KLFAMO/relock_Artiq/kicad/AD DA module.kicad_sch

## KiCad design kicad/AD DA module.kicad_sch (2025-12-02)

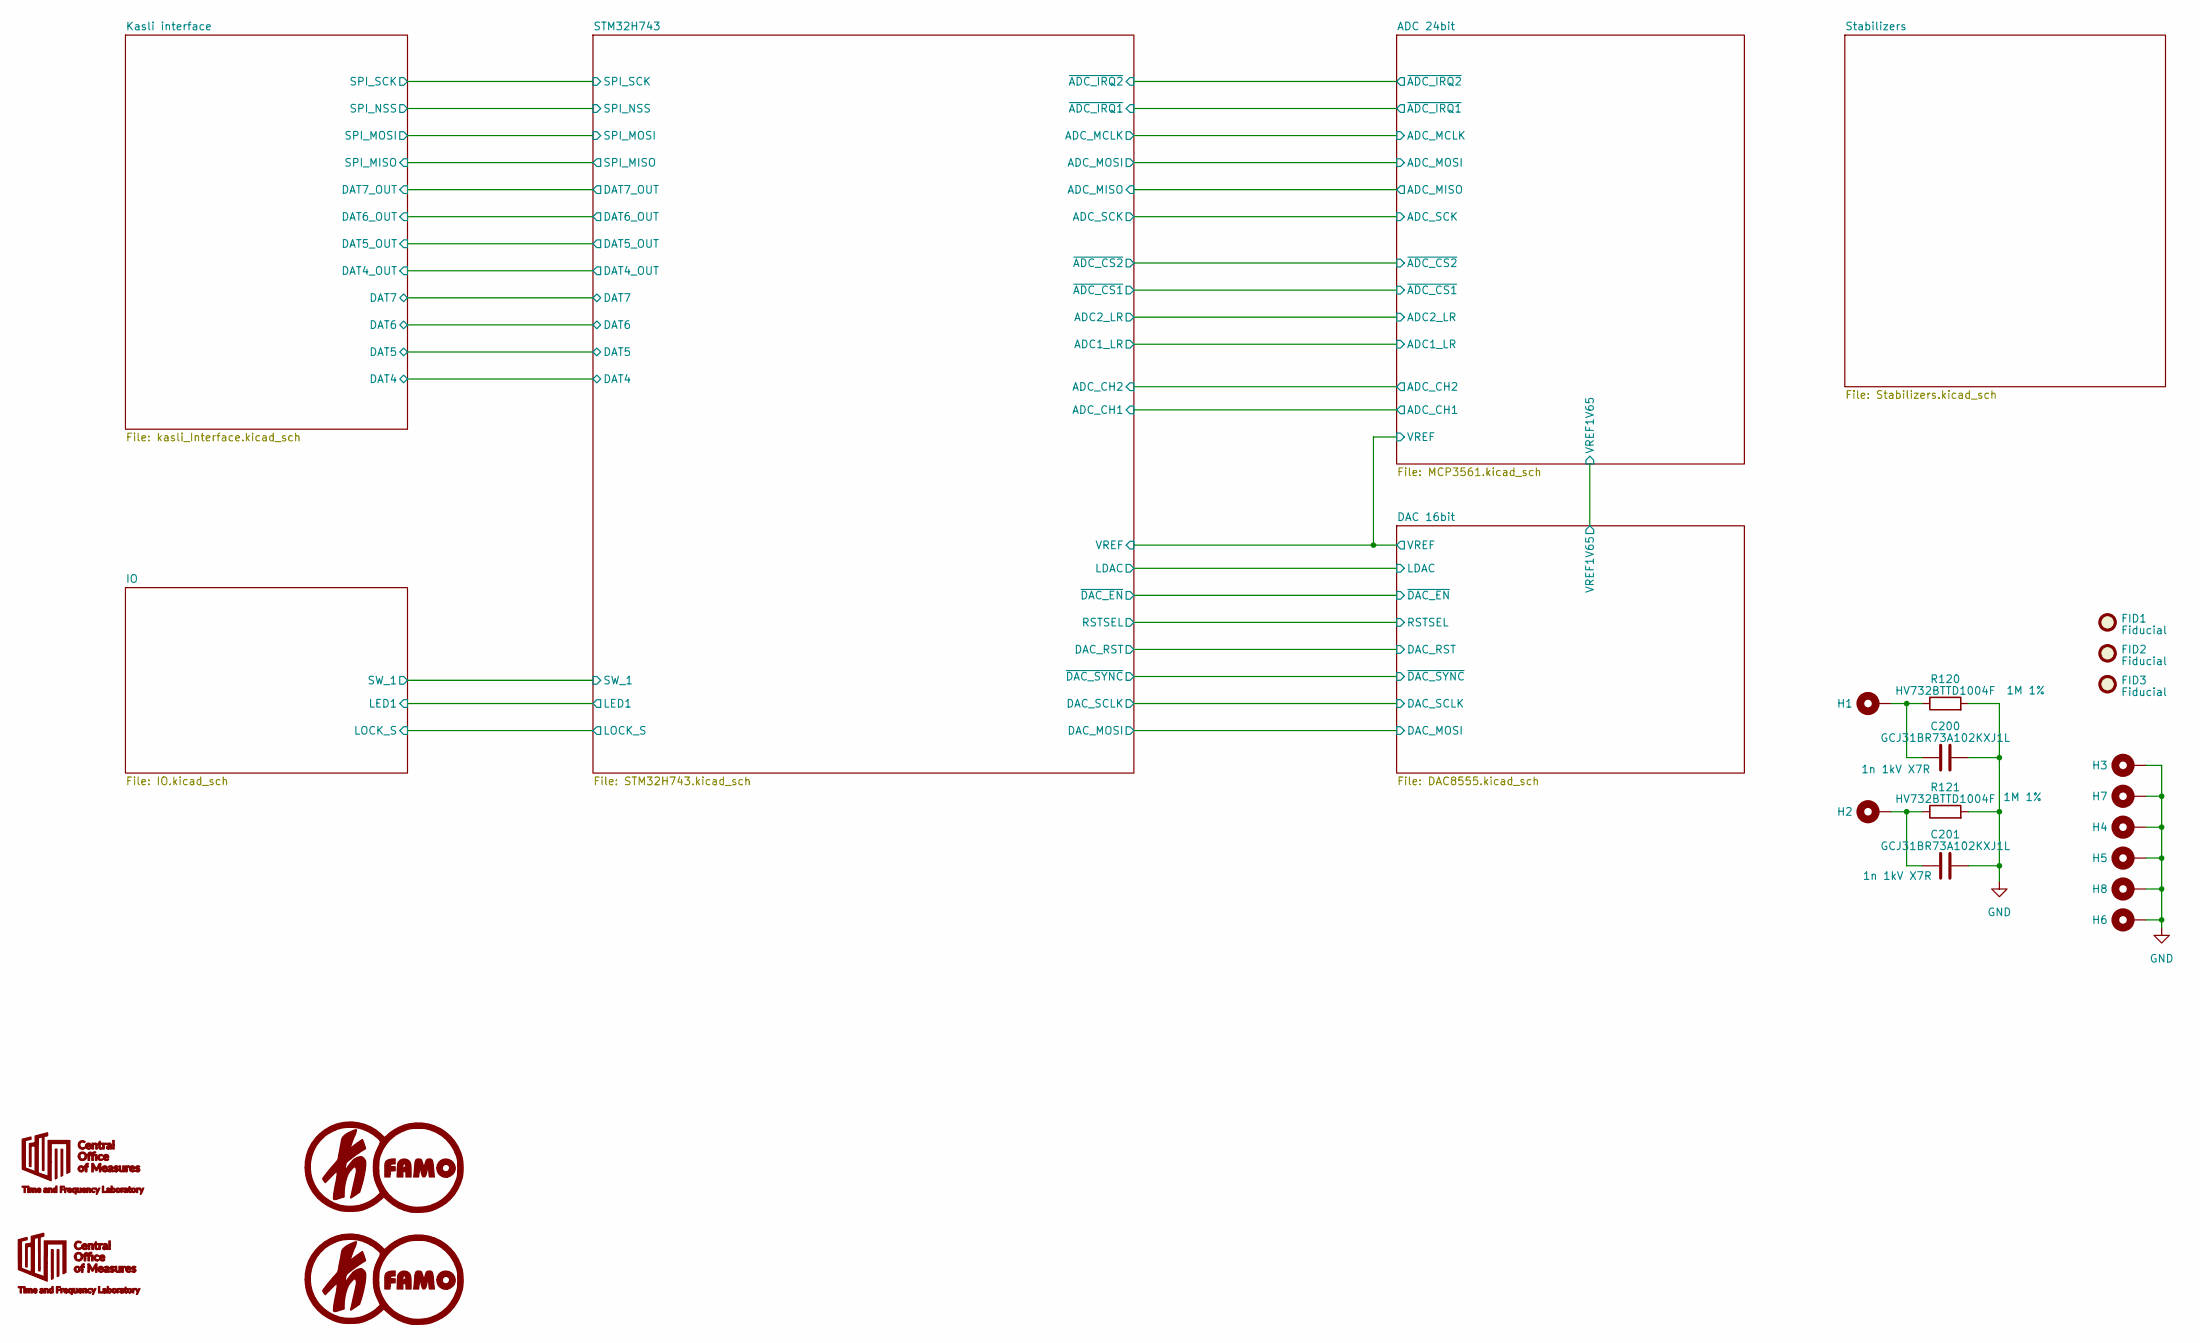
[picture p2: schematic AD DA module.kicad_sch]

Parts:
C200, C201: GCJ31BR73A102KXJ1L; C_1206_3216Metric
FID1, FID2, FID3: Fiducial; Fiducial_0.5mm_Mask1.5mm
G1, G2: LOGO; GUM_logo
G3, G4: LOGO; kl_famo_logo_small
H1, H2: MountingHole_Pad; MountingHole_2.7mm_M2.5_DIN965_Pad
H3, H4, H5, H6, H7, H8: MountingHole_Pad; MountingHole_3.2mm_M3_DIN965_Pad
R120, R121: HV732BTTD1004F; R_1206_3216Metric

Connections:
GND: C200.2, C201.2, H3.1, H4.1, H5.1, H6.1, H7.1, H8.1, R120.2, R121.2
unnamed: C200.1, H1.1, R120.1
unnamed: C201.1, H2.1, R121.1
