KLFAMO/relock_Artiq/kicad/DAC8555.kicad_sch

## KiCad design kicad/DAC8555.kicad_sch (2025-12-02)

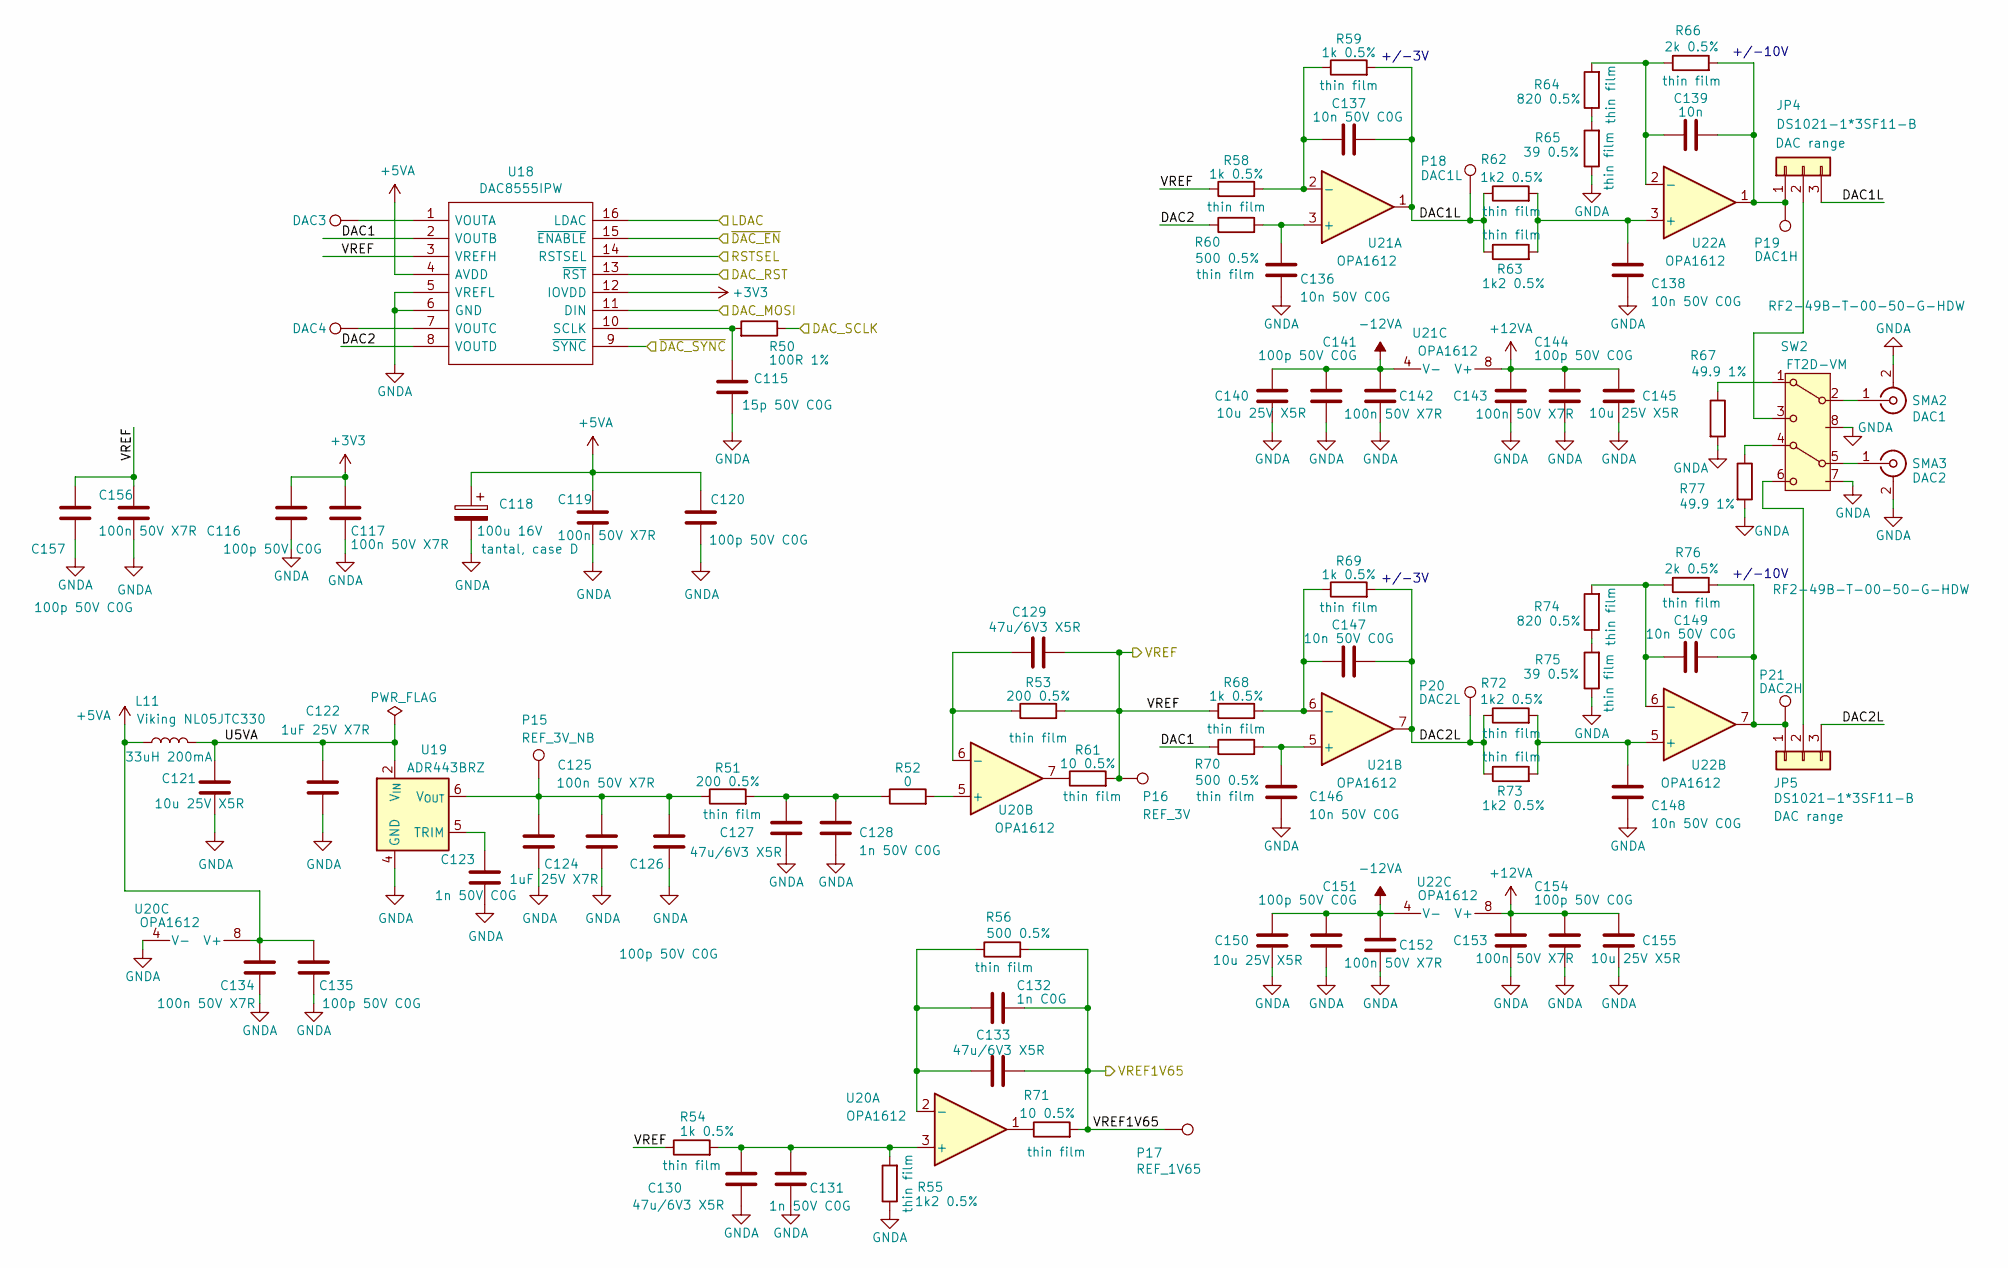
[picture p3: schematic DAC8555.kicad_sch]

Parts:
C115: 15p 50V C0G; C_0603_1608Metric
C116, C120, C126, C135, C141, C144, C151, C154, C157: 100p 50V C0G; C_0603_1608Metric
C117, C119, C125, C134, C142, C143, C152, C153, C156: 100n 50V X7R; C_0603_1608Metric
C118: 100u 16V; CP_EIA-7343-31_Kemet-D
C121, C140, C145, C150, C155: GRM188R61E106KA73D; C_0603_1608Metric
C122, C124: GCM188R71E105KA64J; C_0603_1608Metric
C123, C128, C131: 1n 50V C0G; C_0603_1608Metric
C127, C129, C130, C133: GRM188R60J476ME15D; C_0603_1608Metric
C132: 1n C0G; C_0603_1608Metric
C136, C137, C138, C146, C147, C148, C149: 10n 50V C0G; C_0603_1608Metric
C139: 10n; C_0603_1608Metric
DAC3, DAC4: TestPoint; TestPoint_THTPad_1.5x1.5mm_Drill0.7mm
JP4, JP5: DS1021-1*3SF11-B; PinHeader_1x03_P2.54mm_Vertical
L11: Viking NL05JTC330; L_0805_2012Metric
P15: REF_3V_NB; TestPoint_THTPad_1.5x1.5mm_Drill0.7mm
P16: REF_3V; TestPoint_THTPad_1.5x1.5mm_Drill0.7mm
P17: REF_1V65; TestPoint_THTPad_1.5x1.5mm_Drill0.7mm
P18: DAC1L; TestPoint_THTPad_1.5x1.5mm_Drill0.7mm
P19: DAC1H; TestPoint_THTPad_1.5x1.5mm_Drill0.7mm
P20: DAC2L; TestPoint_THTPad_1.5x1.5mm_Drill0.7mm
P21: DAC2H; TestPoint_THTPad_1.5x1.5mm_Drill0.7mm
R50: 100R 1%; R_0603_1608Metric
R51, R53: 200 0.5%; R_0805_2012Metric_Pad1.20x1.40mm_HandSolder
R52: 0; R_0603_1608Metric
R54, R58, R59, R68, R69: 1k 0.5%; R_0805_2012Metric_Pad1.20x1.40mm_HandSolder
R55, R62, R63, R72, R73: 1k2 0.5%; R_0805_2012Metric_Pad1.20x1.40mm_HandSolder
R56, R60, R70: 500 0.5%; R_0805_2012Metric_Pad1.20x1.40mm_HandSolder
R61, R71: 10 0.5%; R_0805_2012Metric_Pad1.20x1.40mm_HandSolder
R64, R74: 820 0.5%; R_0805_2012Metric_Pad1.20x1.40mm_HandSolder
R65, R75: 39 0.5%; R_0805_2012Metric_Pad1.20x1.40mm_HandSolder
R66, R76: 2k 0.5%; R_0805_2012Metric_Pad1.20x1.40mm_HandSolder
R67, R77: 49.9 1%; R_0603_1608Metric
SMA2, SMA3: RF2-49B-T-00-50-G-HDW; SMA_Amphenol_901-143_Horizontal
SW2: FT2D-VM
U18: DAC8555IPW; TSSOP-16_4.4x5mm_P0.65mm
U19: ADR443BRZ; SOIC-8_3.9x4.9mm_P1.27mm
U20, U21, U22: OPA1612; SOIC-8_3.9x4.9mm_P1.27mm

Connections:
+3V3: C116.1, C117.1, U18.12 (IOVDD)
+5VA: C118.1, C119.1, C120.1, C134.1, C135.1, L11.1, U18.4 (AVDD), U20.8 (V+)
+12VA: C143.1, C144.1, C145.1, C153.1, C154.1, C155.1, U21.8 (V+), U22.8 (V+)
-12VA: C140.1, C141.1, C142.1, C150.1, C151.1, C152.1, U21.4 (V-), U22.4 (V-)
DAC1: R70.1, U18.2 (VOUTB)
DAC1L: C137.2, JP4.3, P18.1, R59.2, R62.1, R63.1, U21.1
DAC2: R60.1, U18.8 (VOUTD)
DAC2L: C147.2, JP5.3, P20.1, R69.2, R72.1, R73.1, U21.7
DAC_MOSI: U18.11 (DIN)
DAC_RST: U18.13 (~RST)
DAC_SCLK: R50.1
GNDA: C115.2, C116.2, C117.2, C118.2, C119.2, C120.2, C121.2, C122.2, C123.1, C124.2, C125.2, C126.2, C127.1, C128.2, C130.1, C131.2, C134.2, C135.2, C136.1, C138.1, C140.2, C141.2, C142.2, C143.2, C144.2, C145.2, C146.1, C148.1, C150.2, C151.2, C152.2, C153.2, C154.2, C155.2, C156.2, C157.2, R55.1, R65.1, R67.2, R75.1, R77.2, SMA2.2 (Ext), SMA3.2 (Ext), SW2.7, SW2.8, U18.5 (VREFL), U18.6 (GND), U19.4 (GND), U20.4 (V-)
LDAC: U18.16 (LDAC)
unnamed: C115.1, R50.2, U18.10 (SCLK)
unnamed: C123.2, U19.5 (TRIM)
unnamed: C124.1, C125.1, C126.1, P15.1, R51.1, U19.6 (V_{OUT})
unnamed: C127.2, C128.1, R51.2, R52.1
unnamed: C129.2, R53.1, U20.6 (-)
unnamed: C130.2, C131.1, R54.2, R55.2, U20.3 (+)
unnamed: C132.1, C133.2, R56.1, U20.2 (-)
unnamed: C136.2, R60.2, U21.3 (+)
unnamed: C137.1, R58.2, R59.1, U21.2 (-)
unnamed: C138.2, R62.2, R63.2, U22.3 (+)
unnamed: C139.1, R64.2, R66.1, U22.2 (-)
unnamed: C139.2, JP4.1, P19.1, R66.2, U22.1
unnamed: C146.2, R70.2, U21.5 (+)
unnamed: C147.1, R68.2, R69.1, U21.6 (-)
unnamed: C148.2, R72.2, R73.2, U22.5 (+)
unnamed: C149.1, R74.2, R76.1, U22.6 (-)
unnamed: C149.2, JP5.1, P21.1, R76.2, U22.7
unnamed: DAC3.1, U18.1 (VOUTA)
unnamed: DAC4.1, U18.7 (VOUTC)
unnamed: JP4.2, SW2.3
unnamed: JP5.2, SW2.6
unnamed: R52.2, U20.5 (+)
unnamed: R61.1, U20.7
unnamed: R64.1, R65.2
unnamed: R67.1, SW2.1
unnamed: R71.1, U20.1
unnamed: R74.1, R75.2
unnamed: R77.1, SW2.4
unnamed: SMA2.1 (In), SW2.2
unnamed: SMA3.1 (In), SW2.5
RSTSEL: U18.14 (RSTSEL)
U5VA: C121.1, C122.1, L11.2, U19.2 (V_{IN})
VREF: C129.1, C156.1, C157.1, P16.1, R53.2, R54.1, R58.1, R61.2, R68.1, U18.3 (VREFH)
VREF1V65: C132.2, C133.1, P17.1, R56.2, R71.2
~DAC_EN: U18.15 (~ENABLE)
~DAC_SYNC: U18.9 (~SYNC)

Notes on the sheet:
+/-3V
+/-10V
