KLFAMO/relock_Artiq/kicad/IO.kicad_sch

## KiCad design kicad/IO.kicad_sch (2025-12-02)

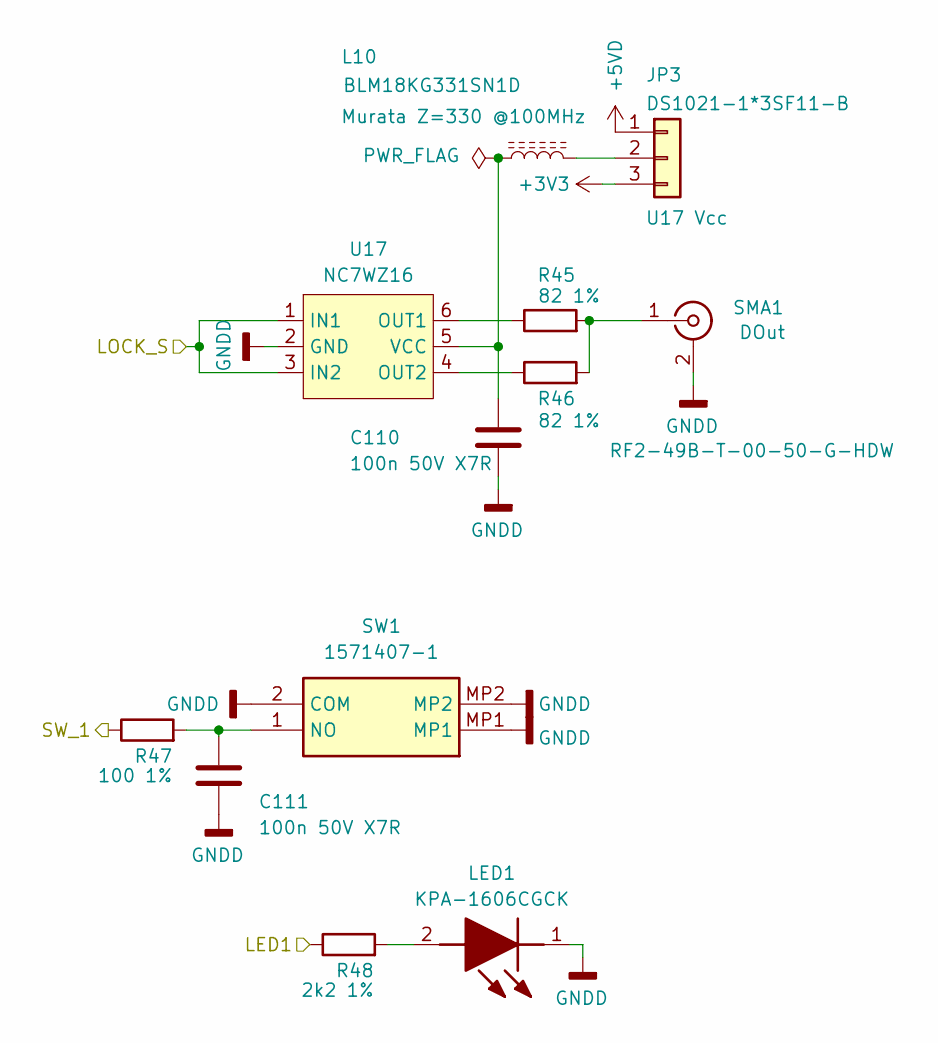
[picture p4: schematic IO.kicad_sch]

Parts:
C110, C111: 100n 50V X7R; C_0603_1608Metric
JP3: DS1021-1*3SF11-B; PinHeader_1x03_P2.54mm_Vertical
L10: BLM18KG331SN1D; L_0603_1608Metric
LED1: KPA-1606CGCK; KPA1606CGCK
R45, R46: 82 1%; R_0603_1608Metric
R47: 100 1%; R_0603_1608Metric
R48: 2k2 1%; R_0603_1608Metric
SMA1: RF2-49B-T-00-50-G-HDW; SMA_Amphenol_901-143_Horizontal
SW1: 1571407-1; 15714071; Manufacturer_Part_Number 1571407-1
U17: NC7WZ16; SOT65P215X100-6N

Connections:
+3V3: JP3.3
+5VD: JP3.1
GNDD: C110.2, C111.2, LED1.1 (K), SMA1.2 (Ext), SW1.2 (COM), SW1.MP1, SW1.MP2, U17.2 (GND)
LED1: R48.1
LOCK_S: U17.1 (IN1), U17.3 (IN2)
unnamed: C110.1, L10.1, U17.5 (VCC)
unnamed: C111.1, R47.2, SW1.1 (NO)
unnamed: JP3.2, L10.2
unnamed: LED1.2 (A), R48.2
unnamed: R45.1, U17.6 (OUT1)
unnamed: R45.2, R46.2, SMA1.1 (In)
unnamed: R46.1, U17.4 (OUT2)
SW_1: R47.1
