KLFAMO/relock_Artiq/kicad/MCP3561.kicad_sch

## KiCad design kicad/MCP3561.kicad_sch (2025-12-02)

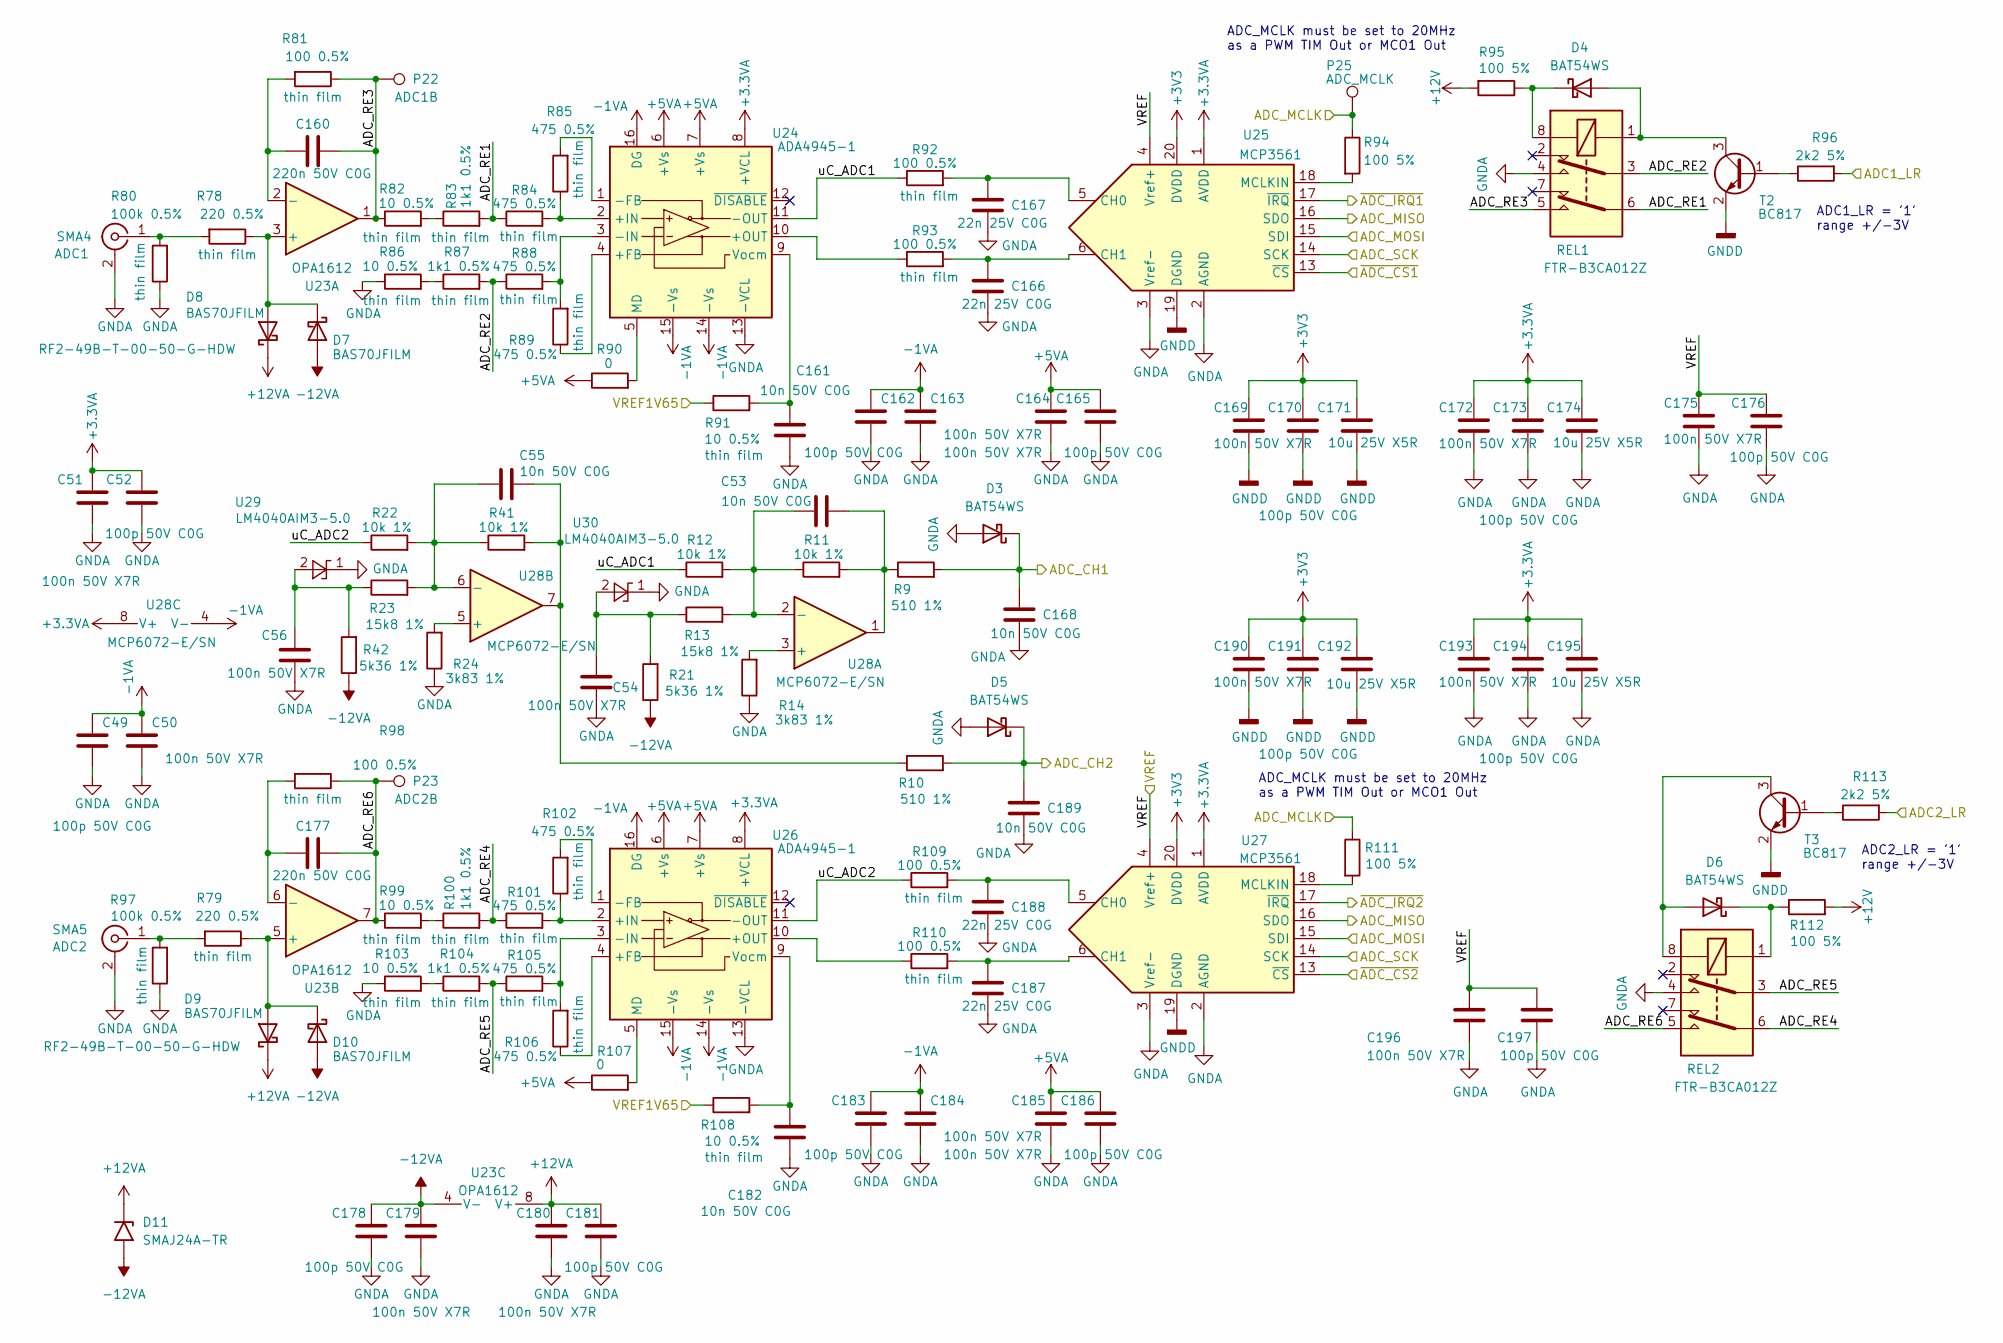
[picture p5: schematic MCP3561.kicad_sch]

Parts:
C49, C52, C162, C165, C170, C173, C176, C178, C181, C183, C186, C191, C194, C197: 100p 50V C0G; C_0603_1608Metric
C50, C51, C54, C56, C163, C164, C169, C172, C175, C179, C180, C184, C185, C190, C193, C196: 100n 50V X7R; C_0603_1608Metric
C53, C55, C161, C168, C182, C189: 10n 50V C0G; C_0603_1608Metric
C160, C177: 220n 50V C0G; C_1206_3216Metric
C166, C167, C187, C188: 22n 25V C0G; C_0603_1608Metric
C171, C174, C192, C195: GRM188R61E106KA73D; C_0603_1608Metric
D3, D4, D5, D6: BAT54WS; D_SOD-323F
D7, D8, D9, D10: BAS70JFILM; D_SOD-323F
D11: SMAJ24A-TR; D_SMA
P22: ADC1B; TestPoint_THTPad_1.5x1.5mm_Drill0.7mm
P23: ADC2B; TestPoint_THTPad_1.5x1.5mm_Drill0.7mm
P25: ADC_MCLK; TestPoint_THTPad_1.5x1.5mm_Drill0.7mm
R9, R10: 510 1%; R_0603_1608Metric
R11, R12, R22, R41: 10k 1%; R_0603_1608Metric
R13, R23: 15k8 1%; R_0603_1608Metric
R14, R24: 3k83 1%; R_0603_1608Metric
R21, R42: 5k36 1%; R_0603_1608Metric
R78, R79: 220 0.5%; R_0603_1608Metric_Pad0.98x0.95mm_HandSolder
R80, R97: 100k 0.5%; R_0805_2012Metric_Pad1.20x1.40mm_HandSolder
R81, R98: 100 0.5%; R_0603_1608Metric_Pad0.98x0.95mm_HandSolder
R82, R86, R91, R99, R103, R108: 10 0.5%; R_0805_2012Metric_Pad1.20x1.40mm_HandSolder
R83, R87, R100, R104: 1k1 0.5%; R_0805_2012Metric_Pad1.20x1.40mm_HandSolder
R84, R85, R88, R89, R101, R102, R105, R106: 475 0.5%; R_0805_2012Metric_Pad1.20x1.40mm_HandSolder
R90, R107: 0; R_0603_1608Metric
R92, R93, R109, R110: 100 0.5%; R_0805_2012Metric_Pad1.20x1.40mm_HandSolder
R94, R111: 100 5%; R_0603_1608Metric
R95, R112: 100 5%; R_1206_3216Metric
R96, R113: 2k2 5%; R_0603_1608Metric
REL1, REL2: FTR-B3CA012Z; FTRB3CA012Z
SMA4, SMA5: RF2-49B-T-00-50-G-HDW; SMA_Amphenol_901-143_Horizontal
T2, T3: BC817; SOT-23
U23: OPA1612; SOIC-8_3.9x4.9mm_P1.27mm
U24, U26: ADA4945-1; LFCSP-16-1EP_3x3mm_P0.5mm_EP1.6x1.6mm_ThermalVias
U25, U27: MCP3561; SSOP-20_4.4x6.5mm_P0.65mm
U28: MCP6072-E/SN; SOIC-8_3.9x4.9mm_P1.27mm
U29, U30: LM4040AIM3-5.0; SOT-23

Connections:
+3.3VA: C51.1, C52.2, C172.1, C173.1, C174.1, C193.1, C194.1, C195.1, U24.8 (+VCL), U25.1 (AVDD), U26.8 (+VCL), U27.1 (AVDD), U28.8 (V+)
+3V3: C169.1, C170.1, C171.1, C190.1, C191.1, C192.1, U25.20 (DVDD), U27.20 (DVDD)
+5VA: C164.1, C165.2, C185.1, C186.2, R90.1, R107.1, U24.6 (+Vs), U24.7 (+Vs), U26.6 (+Vs), U26.7 (+Vs)
+12V: R95.2, R112.2
+12VA: C180.1, C181.2, D8.1 (K), D9.1 (K), D11.1 (A1), U23.8 (V+)
-1VA: C49.2, C50.1, C162.2, C163.1, C183.2, C184.1, U24.14 (-Vs), U24.15 (-Vs), U24.16 (DG), U24.17 (-Vs), U26.14 (-Vs), U26.15 (-Vs), U26.16 (DG), U26.17 (-Vs), U28.4 (V-)
-12VA: C178.2, C179.1, D7.2 (A), D10.2 (A), D11.2 (A2), R21.1, R42.1, U23.4 (V-)
ADC1_LR: R96.2
ADC2_LR: R113.2
ADC_CH1: C168.2, D3.1 (K), R9.2
ADC_CH2: C189.2, D5.1 (K), R10.2
ADC_MCLK: P25.1, R94.1, R111.1
ADC_MISO: U25.16 (SDO), U27.16 (SDO)
ADC_MOSI: U25.15 (SDI), U27.15 (SDI)
ADC_RE1: R83.2, R84.1, REL1.6
ADC_RE2: R87.2, R88.1, REL1.3
ADC_RE3: C160.2, P22.1, R81.1, R82.1, REL1.5, U23.1
ADC_RE4: R100.2, R101.1, REL2.6
ADC_RE5: R104.2, R105.1, REL2.3
ADC_RE6: C177.2, P23.1, R98.1, R99.1, REL2.5, U23.7
ADC_SCK: U25.14 (SCK), U27.14 (SCK)
GNDA: C49.1, C50.2, C51.2, C52.1, C54.2, C56.2, C161.2, C162.1, C163.2, C164.2, C165.1, C166.1, C167.1, C168.1, C172.2, C173.2, C174.2, C175.2, C176.2, C178.1, C179.2, C180.2, C181.1, C182.2, C183.1, C184.2, C185.2, C186.1, C187.1, C188.1, C189.1, C193.2, C194.2, C195.2, C196.2, C197.2, D3.2 (A), D5.2 (A), R14.1, R24.1, R80.1, R86.1, R97.1, R103.1, REL1.4, REL2.4, SMA4.2 (Ext), SMA5.2 (Ext), U24.13 (-VCL), U25.2 (AGND), U25.3 (Vref-), U26.13 (-VCL), U27.2 (AGND), U27.3 (Vref-), U29.1 (K), U30.1 (K)
GNDD: C169.2, C170.2, C171.2, C190.2, C191.2, C192.2, T2.2 (E), T3.2 (E), U25.19 (DGND), U27.19 (DGND)
unnamed: C53.1, R9.1, R11.2, U28.1
unnamed: C53.2, R11.1, R12.2, R13.2, U28.2 (-)
unnamed: C54.1, R13.1, R21.2, U30.2 (A)
unnamed: C55.1, R10.1, R41.2, U28.7
unnamed: C55.2, R22.2, R23.2, R41.1, U28.6 (-)
unnamed: C56.1, R23.1, R42.2, U29.2 (A)
unnamed: C160.1, R81.2, U23.2 (-)
unnamed: C161.1, R91.2, U24.9 (Vocm)
unnamed: C166.2, R93.2, U25.6 (CH1)
unnamed: C167.2, R92.2, U25.5 (CH0)
unnamed: C177.1, R98.2, U23.6 (-)
unnamed: C182.1, R108.2, U26.9 (Vocm)
unnamed: C187.2, R110.2, U27.6 (CH1)
unnamed: C188.2, R109.2, U27.5 (CH0)
unnamed: D4.1 (K), R95.1, REL1.8
unnamed: D4.2 (A), REL1.1, T2.3 (C)
unnamed: D6.1 (K), R112.1, REL2.1
unnamed: D6.2 (A), REL2.8, T3.3 (C)
unnamed: D7.1 (K), D8.2 (A), R78.1, U23.3 (+)
unnamed: D9.2 (A), D10.1 (K), R79.1, U23.5 (+)
unnamed: R14.2, U28.3 (+)
unnamed: R24.2, U28.5 (+)
unnamed: R78.2, R80.2, SMA4.1 (In)
unnamed: R79.2, R97.2, SMA5.1 (In)
unnamed: R82.2, R83.1
unnamed: R84.2, R85.1, U24.2 (+IN)
unnamed: R85.2, U24.1 (-FB)
unnamed: R86.2, R87.1
unnamed: R88.2, R89.2, U24.3 (-IN)
unnamed: R89.1, U24.4 (+FB)
unnamed: R90.2, U24.5 (MD)
unnamed: R93.1, U24.10 (+OUT)
unnamed: R94.2, U25.18 (MCLKIN)
unnamed: R96.1, T2.1 (B)
unnamed: R99.2, R100.1
unnamed: R101.2, R102.1, U26.2 (+IN)
unnamed: R102.2, U26.1 (-FB)
unnamed: R103.2, R104.1
unnamed: R105.2, R106.2, U26.3 (-IN)
unnamed: R106.1, U26.4 (+FB)
unnamed: R107.2, U26.5 (MD)
unnamed: R110.1, U26.10 (+OUT)
unnamed: R111.2, U27.18 (MCLKIN)
unnamed: R113.1, T3.1 (B)
VREF: C175.1, C176.1, C196.1, C197.1, U25.4 (Vref+), U27.4 (Vref+)
VREF1V65: R91.1, R108.1
uC_ADC1: R12.1, R92.1, U24.11 (-OUT)
uC_ADC2: R22.1, R109.1, U26.11 (-OUT)
~ADC_CS1: U25.13 (~CS)
~ADC_CS2: U27.13 (~CS)
~ADC_IRQ1: U25.17 (~IRQ)
~ADC_IRQ2: U27.17 (~IRQ)

Notes on the sheet:
ADC2_LR = '1' range +/-3V
ADC_MCLK must be set to 20MHz as a PWM TIM Out or MCO1 Out
ADC1_LR = '1' range +/-3V
