KLFAMO/relock_Artiq/kicad/STM32H743.kicad_sch

## KiCad design kicad/STM32H743.kicad_sch (2025-12-02)

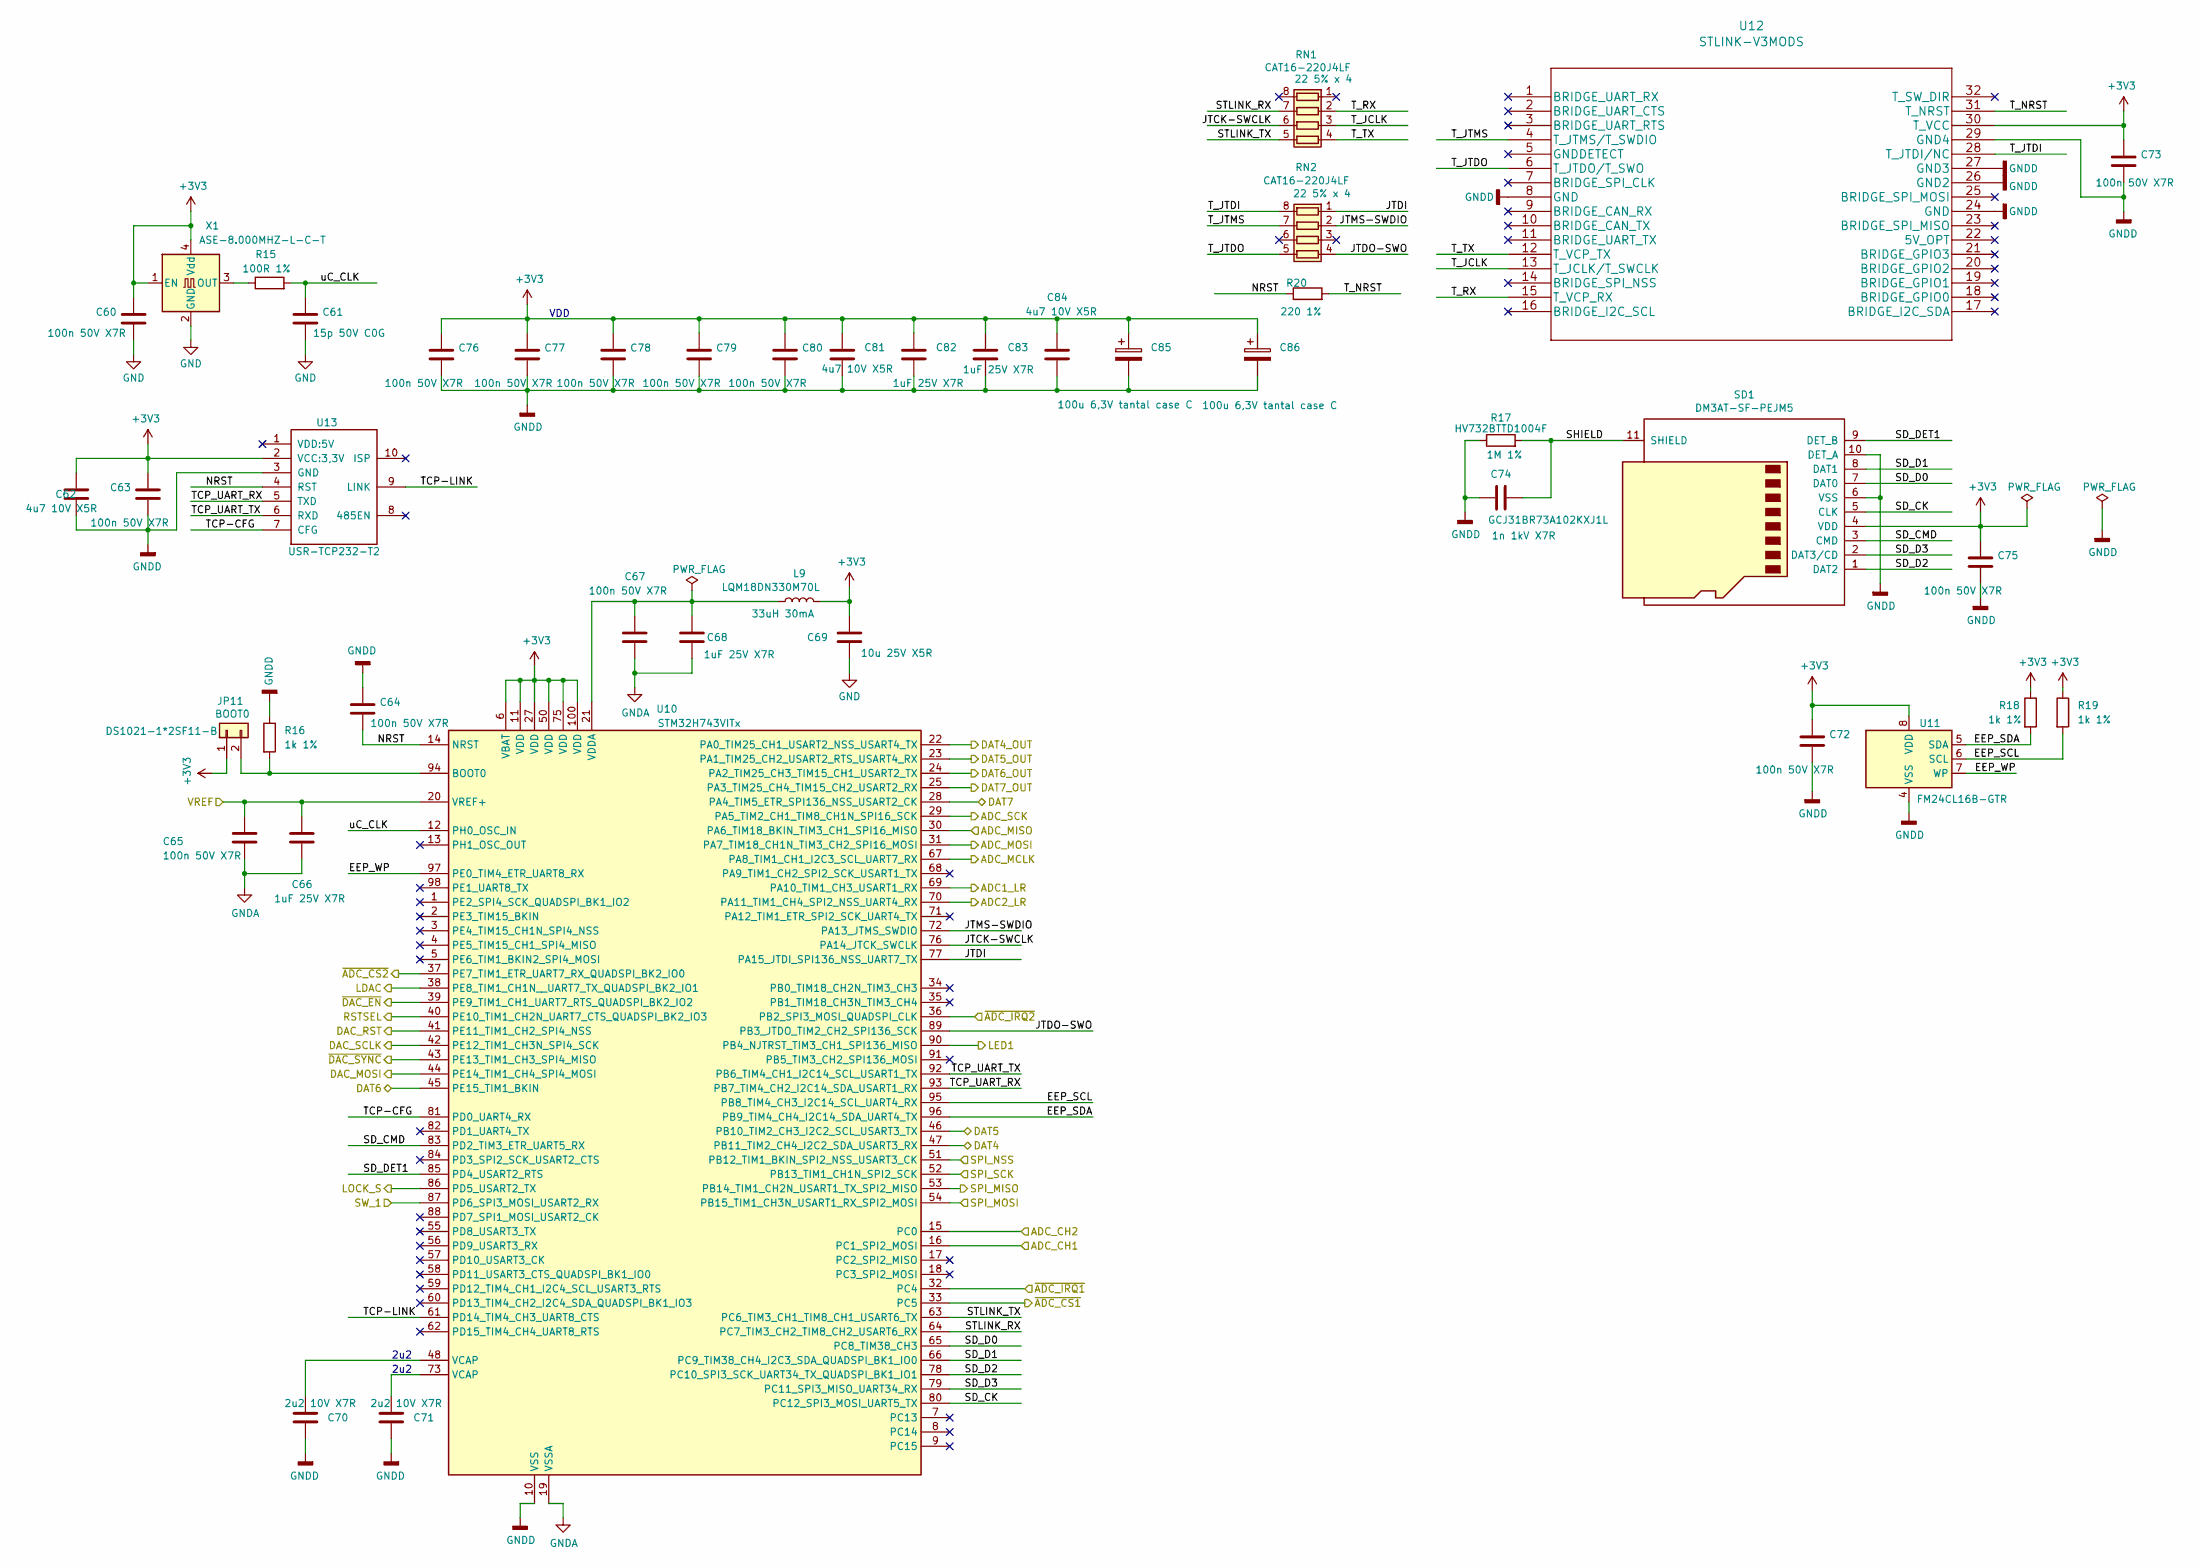
[picture p6: schematic STM32H743.kicad_sch]

Parts:
C60, C63, C64, C65, C67, C72, C73, C75, C76, C77, C78, C79, C80: 100n 50V X7R; C_0603_1608Metric
C61: 15p 50V C0G; C_0603_1608Metric
C62, C81, C84: 4u7 10V X5R; C_0603_1608Metric
C66, C68, C82, C83: GCM188R71E105KA64J; C_0603_1608Metric
C69: GRM188R61E106KA73D; C_0603_1608Metric
C70, C71: 2u2 10V X7R; C_0603_1608Metric
C74: GCJ31BR73A102KXJ1L; C_1206_3216Metric
C85, C86: 293D107X9010C2TE3; CP_EIA-7132-28_AVX-C
JP11: DS1021-1*2SF11-B; PinHeader_1x02_P2.54mm_Vertical
L9: LQM18DN330M70L; L_0603_1608Metric
R15: 100R 1%; R_0603_1608Metric
R16, R18, R19: 1k 1%; R_0603_1608Metric
R17: HV732BTTD1004F; R_1206_3216Metric
R20: 220 1%; R_0603_1608Metric
RN1, RN2: CAT16-220J4LF; R_Array_Concave_4x0603
SD1: DM3AT-SF-PEJM5; microSD_HC_Hirose_DM3AT-SF-PEJM5
U10: STM32H743VITx; LQFP-100_14x14mm_P0.5mm
U11: FM24CL16B-GTR; SOIC-8_3.9x4.9mm_P1.27mm
U12: STLINK-V3MODS
U13: USR-TCP232-T2; USR-TC232-T2
X1: ASE-8.000MHZ-L-C-T; Oscillator_SMD_Abracon_ASE-4Pin_3.2x2.5mm

Connections:
+3V3: C60.1, C62.1, C63.1, C69.1, C72.1, C73.1, C75.1, C76.1, C77.1, C78.1, C79.1, C80.1, C81.1, C82.1, C83.1, C84.1, C85.1, C86.1, JP11.1, L9.2, R18.1, R19.1, SD1.4 (VDD), U10.6 (VBAT), U10.11 (VDD), U10.27 (VDD), U10.50 (VDD), U10.75 (VDD), U10.100 (VDD), U11.8 (VDD), U12.30 (T_VCC), U13.2 (VCC:3,3V), X1.1 (EN), X1.4 (Vdd)
ADC1_LR: U10.69 (PA10_TIM1_CH3_USART1_RX)
ADC2_LR: U10.70 (PA11_TIM1_CH4_SPI2_NSS_UART4_RX)
ADC_CH1: U10.16 (PC1_SPI2_MOSI)
ADC_CH2: U10.15 (PC0)
ADC_MCLK: U10.67 (PA8_TIM1_CH1_I2C3_SCL_UART7_RX)
ADC_MISO: U10.30 (PA6_TIM18_BKIN_TIM3_CH1_SPI16_MISO)
ADC_MOSI: U10.31 (PA7_TIM18_CH1N_TIM3_CH2_SPI16_MOSI)
ADC_SCK: U10.29 (PA5_TIM2_CH1_TIM8_CH1N_SPI16_SCK)
DAC_MOSI: U10.44 (PE14_TIM1_CH4_SPI4_MOSI)
DAC_RST: U10.41 (PE11_TIM1_CH2_SPI4_NSS)
DAC_SCLK: U10.42 (PE12_TIM1_CH3N_SPI4_SCK)
DAT4: U10.47 (PB11_TIM2_CH4_I2C2_SDA_USART3_RX)
DAT4_OUT: U10.22 (PA0_TIM25_CH1_USART2_NSS_USART4_TX)
DAT5: U10.46 (PB10_TIM2_CH3_I2C2_SCL_USART3_TX)
DAT5_OUT: U10.23 (PA1_TIM25_CH2_USART2_RTS_USART4_RX)
DAT6: U10.45 (PE15_TIM1_BKIN)
DAT6_OUT: U10.24 (PA2_TIM25_CH3_TIM15_CH1_USART2_TX)
DAT7: U10.28 (PA4_TIM5_ETR_SPI136_NSS_USART2_CK)
DAT7_OUT: U10.25 (PA3_TIM25_CH4_TIM15_CH2_USART2_RX)
EEP_SCL: R19.2, U10.95 (PB8_TIM4_CH3_I2C14_SCL_UART4_RX), U11.6 (SCL)
EEP_SDA: R18.2, U10.96 (PB9_TIM4_CH4_I2C14_SDA_UART4_TX), U11.5 (SDA)
EEP_WP: U10.97 (PE0_TIM4_ETR_UART8_RX), U11.7 (WP)
GND: C60.2, C61.2, C69.2, X1.2 (GND)
GNDA: C65.1, C66.2, C67.1, C68.2, U10.19 (VSSA)
GNDD: C62.2, C63.2, C64.1, C70.1, C71.1, C72.2, C73.2, C74.1, C75.2, C76.2, C77.2, C78.2, C79.2, C80.2, C81.2, C82.2, C83.2, C84.2, C85.2, C86.2, R16.1, R17.1, SD1.6 (VSS), SD1.10 (DET_A), U10.10 (VSS), U10.26 (VSS), U10.49 (VSS), U10.74 (VSS), U10.99 (VSS), U11.4 (VSS), U12.8 (GND), U12.24 (GND), U12.26 (GND2), U12.27 (GND3), U12.29 (GND4), U13.3 (GND)
JTCK-SWCLK: RN1.6 (R3.2), U10.76 (PA14_JTCK_SWCLK)
JTDI: RN2.1 (R1.1), U10.77 (PA15_JTDI_SPI136_NSS_UART7_TX)
JTDO-SWO: RN2.4 (R4.1), U10.89 (PB3_JTDO_TIM2_CH2_SPI136_SCK)
JTMS-SWDIO: RN2.2 (R2.1), U10.72 (PA13_JTMS_SWDIO)
LDAC: U10.38 (PE8_TIM1_CH1N__UART7_TX_QUADSPI_BK2_IO1)
LED1: U10.90 (PB4_NJTRST_TIM3_CH1_SPI136_MISO)
LOCK_S: U10.86 (PD5_USART2_TX)
NRST: C64.2, R20.1, U10.14 (NRST), U13.4 (RST)
unnamed: C67.2, C68.1, L9.1, U10.21 (VDDA)
unnamed: C70.2, U10.48 (VCAP)
unnamed: C71.2, U10.73 (VCAP)
unnamed: JP11.2, R16.2, U10.94 (BOOT0)
unnamed: R15.1, X1.3 (OUT)
RSTSEL: U10.40 (PE10_TIM1_CH2N_UART7_CTS_QUADSPI_BK2_IO3)
SD_CK: SD1.5 (CLK), U10.80 (PC12_SPI3_MOSI_UART5_TX)
SD_CMD: SD1.3 (CMD), U10.83 (PD2_TIM3_ETR_UART5_RX)
SD_D0: SD1.7 (DAT0), U10.65 (PC8_TIM38_CH3)
SD_D1: SD1.8 (DAT1), U10.66 (PC9_TIM38_CH4_I2C3_SDA_QUADSPI_BK1_IO0)
SD_D2: SD1.1 (DAT2), U10.78 (PC10_SPI3_SCK_UART34_TX_QUADSPI_BK1_IO1)
SD_D3: SD1.2 (DAT3/CD), U10.79 (PC11_SPI3_MISO_UART34_RX)
SD_DET1: SD1.9 (DET_B), U10.85 (PD4_USART2_RTS)
SHIELD: C74.2, R17.2, SD1.11 (SHIELD)
SPI_MISO: U10.53 (PB14_TIM1_CH2N_USART1_TX_SPI2_MISO)
SPI_MOSI: U10.54 (PB15_TIM1_CH3N_USART1_RX_SPI2_MOSI)
SPI_NSS: U10.51 (PB12_TIM1_BKIN_SPI2_NSS_USART3_CK)
SPI_SCK: U10.52 (PB13_TIM1_CH1N_SPI2_SCK)
STLINK_RX: RN1.7 (R2.2), U10.64 (PC7_TIM3_CH2_TIM8_CH2_USART6_RX)
STLINK_TX: RN1.5 (R4.2), U10.63 (PC6_TIM3_CH1_TIM8_CH1_USART6_TX)
SW_1: U10.87 (PD6_SPI3_MOSI_USART2_RX)
TCP-CFG: U10.81 (PD0_UART4_RX), U13.7 (CFG)
TCP-LINK: U10.61 (PD14_TIM4_CH3_UART8_CTS), U13.9 (LINK)
TCP_UART_RX: U10.93 (PB7_TIM4_CH2_I2C14_SDA_USART1_RX), U13.5 (TXD)
TCP_UART_TX: U10.92 (PB6_TIM4_CH1_I2C14_SCL_USART1_TX), U13.6 (RXD)
T_JCLK: RN1.3 (R3.1), U12.13 (T_JCLK/T_SWCLK)
T_JTDI: RN2.8 (R1.2), U12.28 (T_JTDI/NC)
T_JTDO: RN2.5 (R4.2), U12.6 (T_JTDO/T_SWO)
T_JTMS: RN2.7 (R2.2), U12.4 (T_JTMS/T_SWDIO)
T_NRST: R20.2, U12.31 (T_NRST)
T_RX: RN1.2 (R2.1), U12.15 (T_VCP_RX)
T_TX: RN1.4 (R4.1), U12.12 (T_VCP_TX)
VREF: C65.2, C66.1, U10.20 (VREF+)
uC_CLK: C61.1, R15.2, U10.12 (PH0_OSC_IN)
~ADC_CS1: U10.33 (PC5)
~ADC_CS2: U10.37 (PE7_TIM1_ETR_UART7_RX_QUADSPI_BK2_IO0)
~ADC_IRQ1: U10.32 (PC4)
~ADC_IRQ2: U10.36 (PB2_SPI3_MOSI_QUADSPI_CLK)
~DAC_EN: U10.39 (PE9_TIM1_CH1_UART7_RTS_QUADSPI_BK2_IO2)
~DAC_SYNC: U10.43 (PE13_TIM1_CH3_SPI4_MISO)

Notes on the sheet:
2u2
VDD
