KLFAMO/relock_Artiq/kicad/Stabilizers.kicad_sch

## KiCad design kicad/Stabilizers.kicad_sch (2025-12-02)

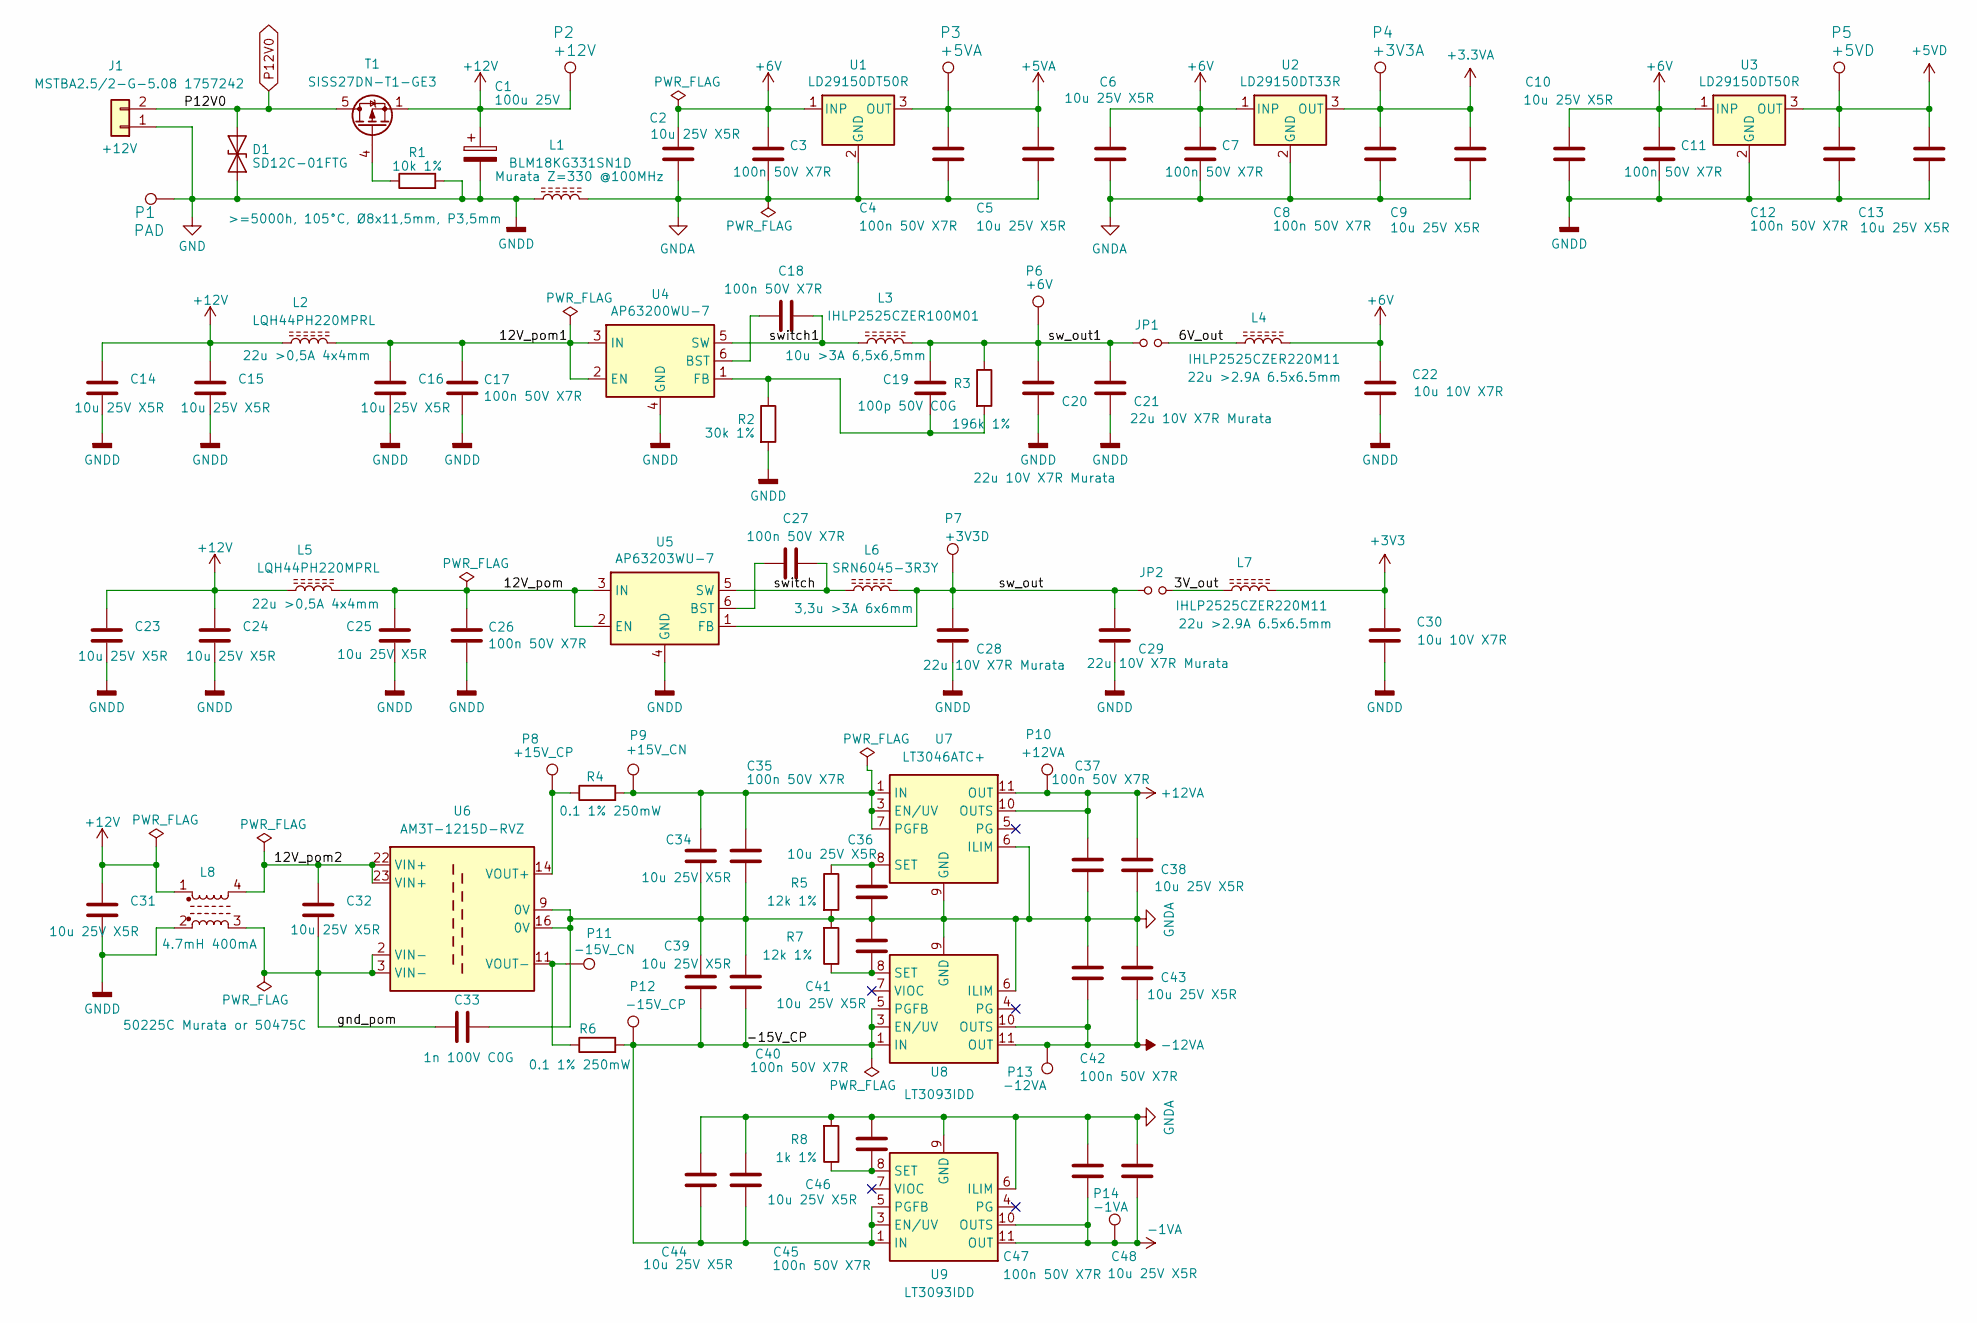
[picture p7: schematic Stabilizers.kicad_sch]

Parts:
C1: 100u 25V; CP_Radial_D8.0mm_P3.50mm
C2, C5, C6, C9, C10, C13, C14, C15, C16, C23, C24, C25, C31, C32, C34, C36, C38, C39, C41, C43, C44, C46, C48: GRM188R61E106KA73D; C_0603_1608Metric
C3, C4, C7, C8, C11, C12, C17, C18, C26, C27, C35, C37, C40, C42, C45, C47: 100n 50V X7R; C_0603_1608Metric
C19: 100p 50V C0G; C_0603_1608Metric
C20, C21, C28, C29: GRM31CR71A226KE15L; C_1206_3216Metric
C22, C30: GRM21BR71A106KA73L; C_0805_2012Metric
C33: MT21N102J101CT; C_0805_2012Metric
D1: SD12C-01FTG; D_SOD-323
J1: MSTBA2.5/2-G-5.08 1757242; PhoenixContact_MSTBA_2,5_2-G-5,08_1x02_P5.08mm_Horizontal
JP1, JP2: 0; R_0603_1608Metric
L1: BLM18KG331SN1D; L_0603_1608Metric
L2, L5: LQH44PH220MPRL; L_MURATA_LQH44
L3: IHLP2525CZER100M01; L_Vishay_IHLP-2525
L4, L7: IHLP2525CZER220M11; L_Vishay_IHLP-2525
L6: SRN6045-3R3Y; L_Bourns-SRN6028
L8: 50225C Murata or 50475C; L_CommonMode_Murata_5000
P1: PAD; TestPoint_Bridge_Pitch2.54mm_Drill1.0mm
P2: +12V; TestPoint_THTPad_1.5x1.5mm_Drill0.7mm
P3: +5VA; TestPoint_THTPad_1.5x1.5mm_Drill0.7mm
P4: +3V3A; TestPoint_THTPad_1.5x1.5mm_Drill0.7mm
P5: +5VD; TestPoint_THTPad_1.5x1.5mm_Drill0.7mm
P6: +6V; TestPoint_THTPad_1.5x1.5mm_Drill0.7mm
P7: +3V3D; TestPoint_THTPad_1.5x1.5mm_Drill0.7mm
P8: +15V_CP; TestPoint_THTPad_1.5x1.5mm_Drill0.7mm
P9: +15V_CN; TestPoint_THTPad_1.5x1.5mm_Drill0.7mm
P10: +12VA; TestPoint_THTPad_1.5x1.5mm_Drill0.7mm
P11: -15V_CN; TestPoint_THTPad_1.5x1.5mm_Drill0.7mm
P12: -15V_CP; TestPoint_THTPad_1.5x1.5mm_Drill0.7mm
P13: -12VA; TestPoint_THTPad_1.5x1.5mm_Drill0.7mm
P14: -1VA; TestPoint_THTPad_1.5x1.5mm_Drill0.7mm
R1: 10k 1%; R_0603_1608Metric
R2: 30k 1%; R_0603_1608Metric
R3: 196k 1%; R_0603_1608Metric
R4, R6: 0.1 1% 250mW; R_0805_2012Metric
R5, R7: 12k 1%; R_0603_1608Metric
R8: 1k 1%; R_0603_1608Metric
T1: SISS27DN-T1-GE3; Diodes_PowerDI3333-8
U1, U3: LD29150DT50R; TO-252-2
U2: LD29150DT33R; TO-252-2
U4: AP63200WU-7; TSOT-23-6
U5: AP63203WU-7; TSOT-23-6
U6: AM3T-1215D-RVZ; AM3T-RVZ
U7: LT3046ATC+; DFN-12-1EP_2x3mm_P0.45mm_EP0.64x2.4mm
U8, U9: LT3093IDD; DFN-12-1EP_2x3mm_P0.45mm_EP0.64x2.4mm

Connections:
3V_out: JP2.1, L7.2
6V_out: JP1.1, L4.2
12V_pom: C25.1, C26.1, L5.1, U5.2 (EN), U5.3 (IN)
12V_pom1: C16.1, C17.1, L2.1, U4.2 (EN), U4.3 (IN)
12V_pom2: C32.1, L8.4, U6.22 (VIN+), U6.23 (VIN+)
+3.3VA: C8.2, C9.1, P4.1, U2.3 (OUT)
+3V3: C30.1, L7.1
+5VA: C4.2, C5.1, P3.1, U1.3 (OUT)
+5VD: C12.2, C13.1, P5.1, U3.3 (OUT)
+6V: C2.1, C3.2, C6.1, C7.2, C10.1, C11.2, C22.1, L4.1, U1.1 (INP), U2.1 (INP), U3.1 (INP)
+12V: C1.1, C14.1, C15.1, C23.1, C24.1, C31.1, L2.2, L5.2, L8.1, P2.1, T1.1 (S), T1.2 (S), T1.3 (S)
+12VA: C37.2, C38.1, P10.1, U7.10 (OUTS), U7.11 (OUT), U7.12 (OUT)
-1VA: C47.2, C48.2, P14.1, U9.10 (OUTS), U9.11 (OUT), U9.12 (OUT)
-12VA: C42.2, C43.2, P13.1, U8.10 (OUTS), U8.11 (OUT), U8.12 (OUT)
-15V_CP: C39.2, C40.1, C44.2, C45.1, P12.1, R6.2, U8.1 (IN), U8.2 (IN), U8.3 (EN/UV), U8.5 (PGFB), U8.13 (IN), U9.1 (IN), U9.2 (IN), U9.3 (EN/UV), U9.5 (PGFB), U9.13 (IN)
GND: C1.2, C10.2, C11.1, C12.1, C13.2, C14.2, C15.2, C16.2, C17.2, C20.2, C21.2, C22.2, C23.2, C24.2, C25.2, C26.2, C28.2, C29.2, C30.2, C31.2, D1.1 (A1), J1.1, L1.1, L8.2, P1.1, R1.2, R2.2, U3.2 (GND), U4.4 (GND), U5.4 (GND)
GNDA: C2.2, C3.1, C4.1, C5.2, C6.2, C7.1, C8.1, C9.2, C33.1, C34.2, C35.2, C36.2, C37.1, C38.2, C39.1, C40.2, C41.2, C42.1, C43.1, C44.1, C45.2, C46.2, C47.1, C48.1, L1.2, R5.2, R7.2, R8.2, U1.2 (GND), U2.2 (GND), U6.9 (0V), U6.16 (0V), U7.6 (ILIM), U7.9 (GND), U7.13 (GND), U8.6 (ILIM), U8.9 (GND), U9.6 (ILIM), U9.9 (GND)
unnamed: C18.2, U4.6 (BST)
unnamed: C19.2, R2.1, R3.2, U4.1 (FB)
unnamed: C27.2, U5.6 (BST)
unnamed: C34.1, C35.1, P9.1, R4.2, U7.1 (IN), U7.2 (IN), U7.3 (EN/UV), U7.7 (PGFB)
unnamed: C36.1, R5.1, U7.8 (SET)
unnamed: C41.1, R7.1, U8.8 (SET)
unnamed: C46.1, R8.1, U9.8 (SET)
unnamed: P8.1, R4.1, U6.14 (VOUT+)
unnamed: P11.1, R6.1, U6.11 (VOUT-)
unnamed: R1.1, T1.4 (G)
P12V0: D1.2 (A2), J1.2, T1.5 (D)
gnd_pom: C32.2, C33.2, L8.3, U6.2 (VIN-), U6.3 (VIN-)
sw_out: C28.1, C29.1, JP2.2, L6.1, P7.1, U5.1 (FB)
sw_out1: C19.1, C20.1, C21.1, JP1.2, L3.1, P6.1, R3.1
switch: C27.1, L6.2, U5.5 (SW)
switch1: C18.1, L3.2, U4.5 (SW)
