KLFAMO/relock_Artiq/kicad/kasli_Interface.kicad_sch

## KiCad design kicad/kasli_Interface.kicad_sch (2025-12-02)

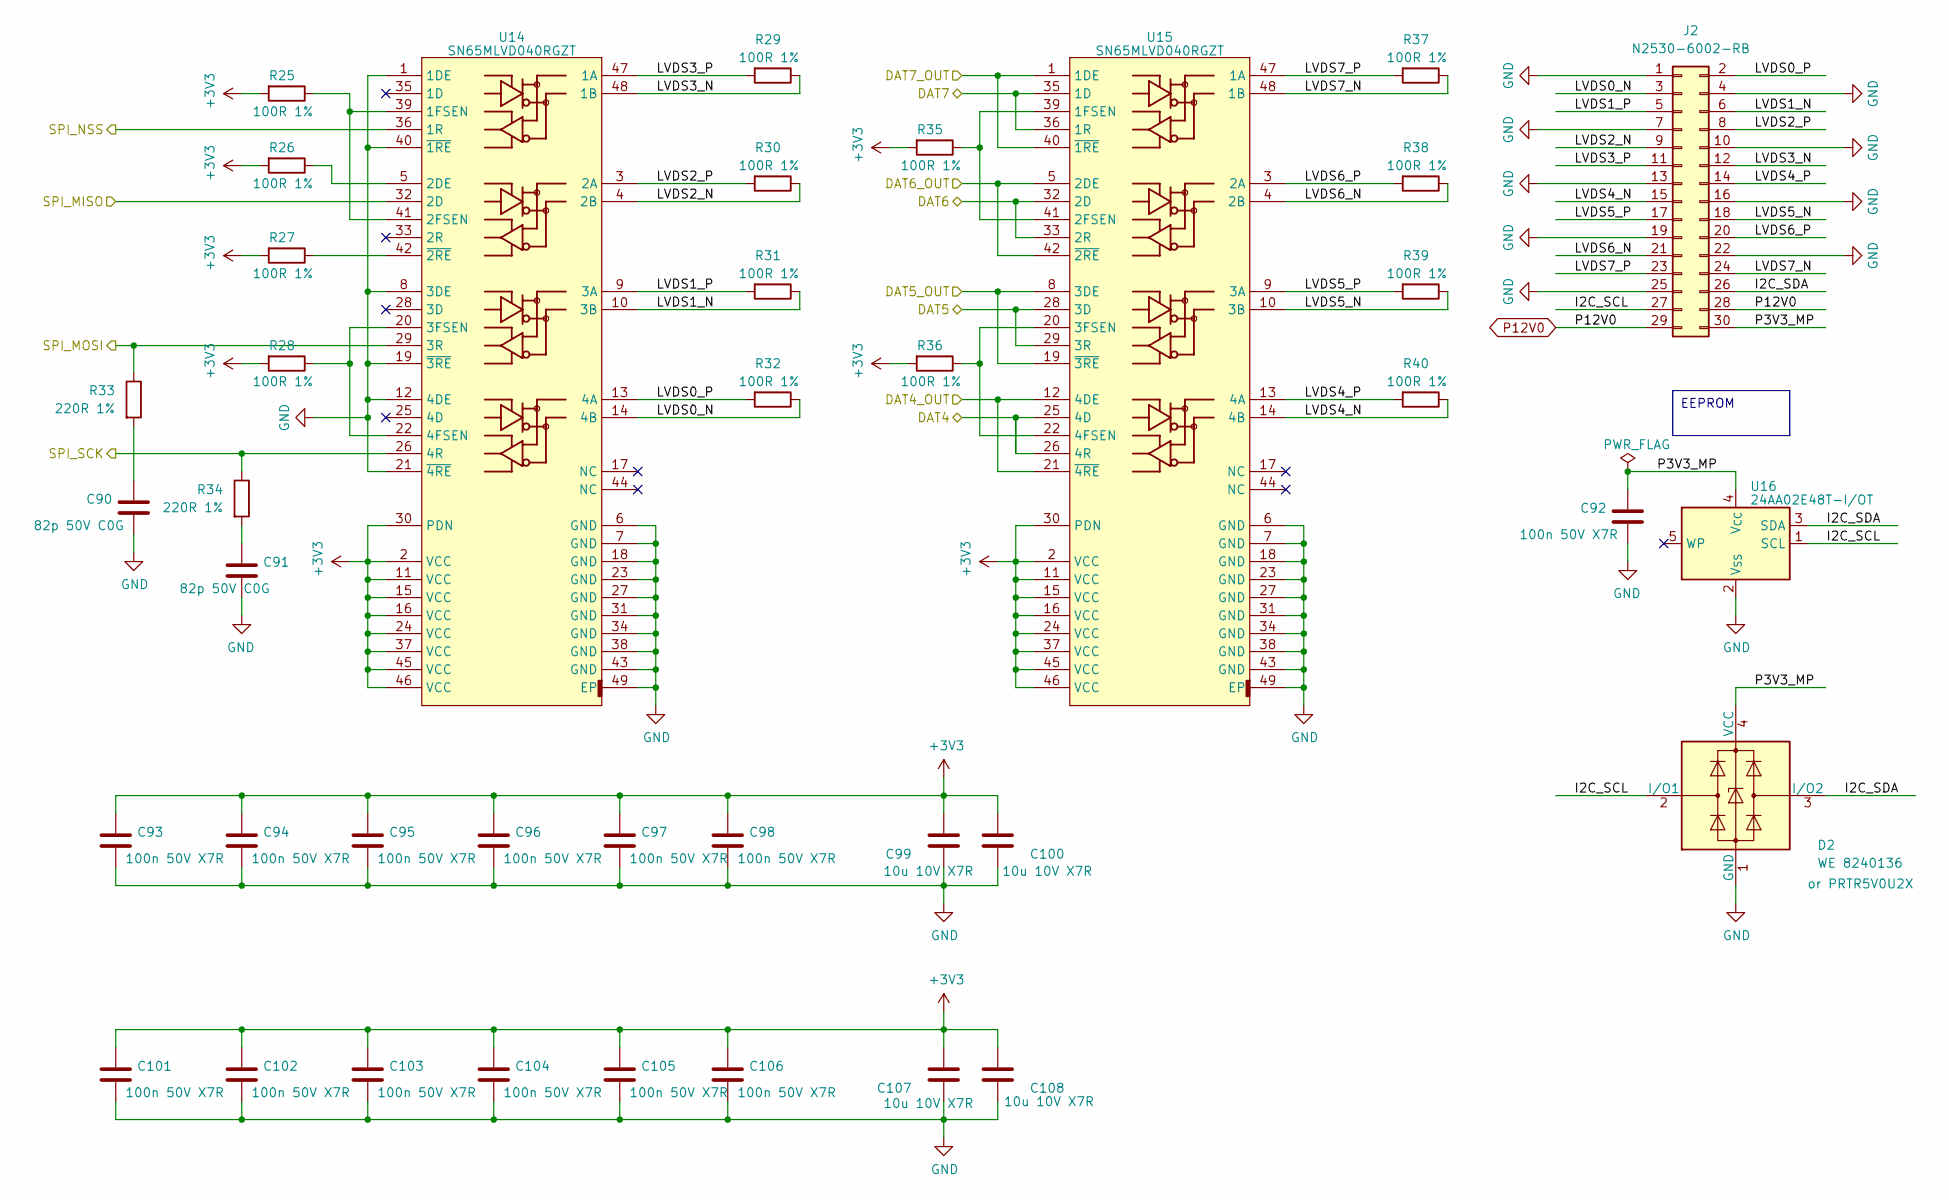
[picture p8: schematic kasli_Interface.kicad_sch]

Parts:
C90, C91: 82p 50V C0G; C_0603_1608Metric
C92, C93, C94, C95, C96, C97, C98, C101, C102, C103, C104, C105, C106: 100n 50V X7R; C_0603_1608Metric
C99, C100, C107, C108: GRM21BR71A106KA73L; C_0805_2012Metric
D2: WE 8240136; SOT-143
J2: N2530-6002-RB; IDC-Header_2x15_P2.54mm_Vertical
R25, R26, R27, R28, R29, R30, R31, R32, R35, R36, R37, R38, R39, R40: 100R 1%; R_0603_1608Metric
R33, R34: 220R 1%; R_0603_1608Metric
U14, U15: SN65MLVD040RGZT; VQFN-48-1EP_7x7mm_P0.5mm_EP4.1x4.1mm_ThermalVias
U16: 24AA02E48T-I/OT; SOT-23-5

Connections:
+3V3: C93.1, C94.1, C95.1, C96.1, C97.1, C98.1, C99.1, C100.1, C101.1, C102.1, C103.1, C104.1, C105.1, C106.1, C107.1, C108.1, R25.2, R26.2, R27.2, R28.2, R35.2, R36.2, U14.2 (VCC), U14.11 (VCC), U14.15 (VCC), U14.16 (VCC), U14.24 (VCC), U14.30 (PDN), U14.37 (VCC), U14.45 (VCC), U14.46 (VCC), U15.2 (VCC), U15.11 (VCC), U15.15 (VCC), U15.16 (VCC), U15.24 (VCC), U15.30 (PDN), U15.37 (VCC), U15.45 (VCC), U15.46 (VCC)
DAT4: U15.25 (4D), U15.26 (4R)
DAT4_OUT: U15.12 (4DE), U15.21 (~4RE)
DAT5: U15.28 (3D), U15.29 (3R)
DAT5_OUT: U15.8 (3DE), U15.19 (~3RE)
DAT6: U15.32 (2D), U15.33 (2R)
DAT6_OUT: U15.5 (2DE), U15.42 (~2RE)
DAT7: U15.35 (1D), U15.36 (1R)
DAT7_OUT: U15.1 (1DE), U15.40 (~1RE)
GND: C90.2, C91.2, C92.2, C93.2, C94.2, C95.2, C96.2, C97.2, C98.2, C99.2, C100.2, C101.2, C102.2, C103.2, C104.2, C105.2, C106.2, C107.2, C108.2, D2.1 (GND), J2.1, J2.4, J2.7, J2.10, J2.13, J2.16, J2.19, J2.22, J2.25, U14.1 (1DE), U14.6 (GND), U14.7 (GND), U14.8 (3DE), U14.12 (4DE), U14.18 (GND), U14.19 (~3RE), U14.21 (~4RE), U14.23 (GND), U14.27 (GND), U14.31 (GND), U14.34 (GND), U14.38 (GND), U14.40 (~1RE), U14.43 (GND), U14.49 (EP), U15.6 (GND), U15.7 (GND), U15.18 (GND), U15.23 (GND), U15.27 (GND), U15.31 (GND), U15.34 (GND), U15.38 (GND), U15.43 (GND), U15.49 (EP), U16.2 (V_{SS})
I2C_SCL: D2.2 (I/O1), J2.27, U16.1 (SCL)
I2C_SDA: D2.3 (I/O2), J2.26, U16.3 (SDA)
LVDS0_N: J2.3, R32.1, U14.14 (4B)
LVDS0_P: J2.2, R32.2, U14.13 (4A)
LVDS1_N: J2.6, R31.1, U14.10 (3B)
LVDS1_P: J2.5, R31.2, U14.9 (3A)
LVDS2_N: J2.9, R30.1, U14.4 (2B)
LVDS2_P: J2.8, R30.2, U14.3 (2A)
LVDS3_N: J2.12, R29.1, U14.48 (1B)
LVDS3_P: J2.11, R29.2, U14.47 (1A)
LVDS4_N: J2.15, R40.1, U15.14 (4B)
LVDS4_P: J2.14, R40.2, U15.13 (4A)
LVDS5_N: J2.18, R39.1, U15.10 (3B)
LVDS5_P: J2.17, R39.2, U15.9 (3A)
LVDS6_N: J2.21, R38.1, U15.4 (2B)
LVDS6_P: J2.20, R38.2, U15.3 (2A)
LVDS7_N: J2.24, R37.1, U15.48 (1B)
LVDS7_P: J2.23, R37.2, U15.47 (1A)
unnamed: C90.1, R33.2
unnamed: C91.1, R34.2
unnamed: R25.1, U14.39 (1FSEN), U14.41 (2FSEN)
unnamed: R26.1, U14.5 (2DE)
unnamed: R27.1, U14.42 (~2RE)
unnamed: R28.1, U14.20 (3FSEN), U14.22 (4FSEN)
unnamed: R35.1, U15.39 (1FSEN), U15.41 (2FSEN)
unnamed: R36.1, U15.20 (3FSEN), U15.22 (4FSEN)
P3V3_MP: C92.1, D2.4 (VCC), J2.30, U16.4 (V_{CC})
P12V0: J2.28, J2.29
SPI_MISO: U14.32 (2D)
SPI_MOSI: R33.1, U14.29 (3R)
SPI_NSS: U14.36 (1R)
SPI_SCK: R34.1, U14.26 (4R)

Notes on the sheet:
EEPROM
